upenn-embedded/final-project-s26-t15/image/README/1773645373201.png

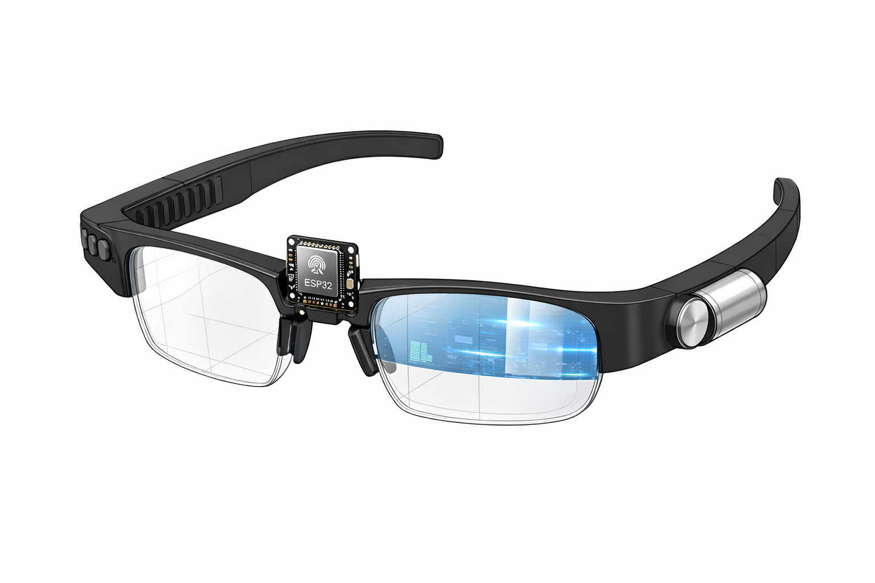
image/README/1773645373201.png
