upenn-embedded/final-project-s26-t15/image/README/1776481041381.png

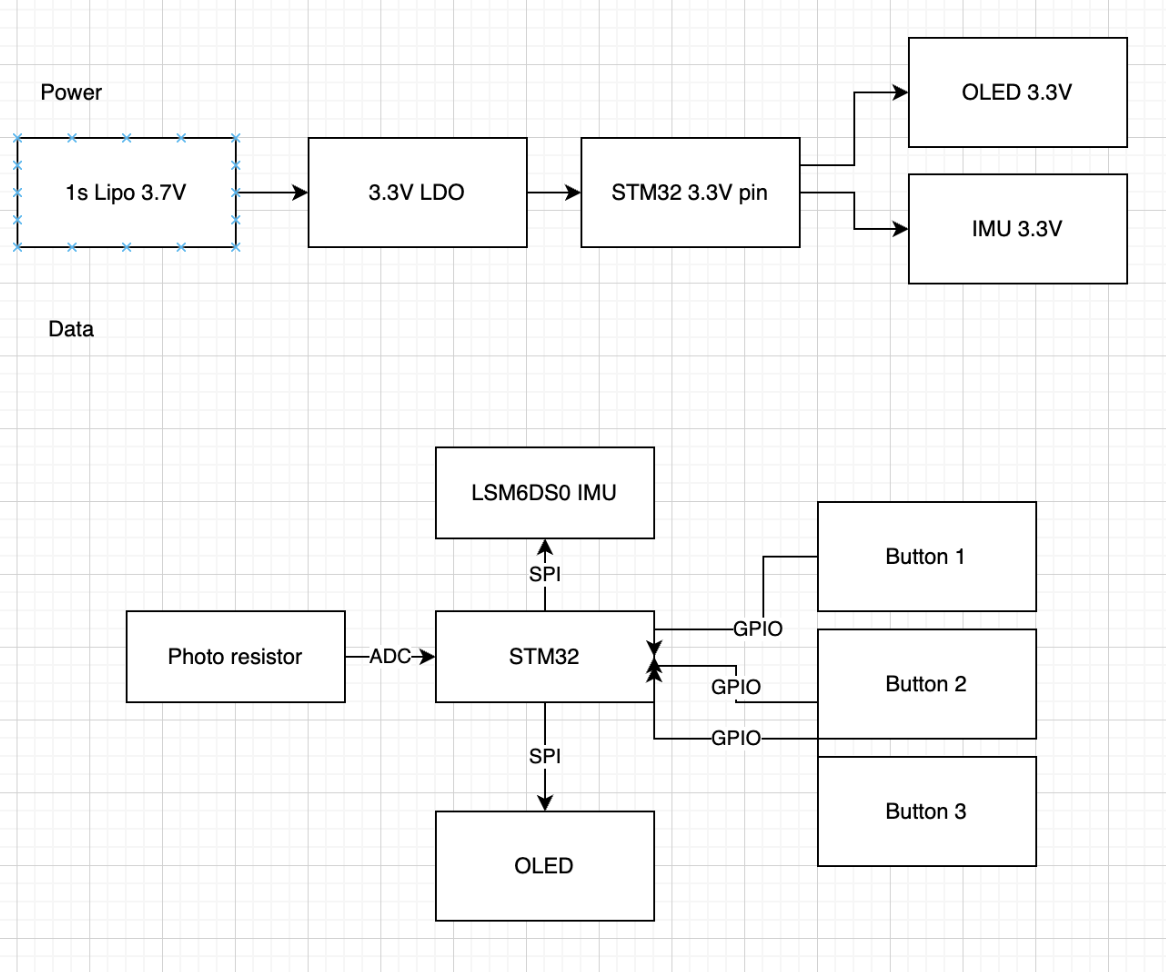
image/README/1776481041381.png
